Antti-Pyhaluoto/GPS-Project-TVT17SPL/GPS/GPS_encode_v1.cpp

#include "mbed.h"
#include <string>
#include "math.h"


Serial gsm(D14, D15);
Serial pc(SERIAL_TX, SERIAL_RX);



int main()
{
    
    pc.baud(9600);
    
    pc.printf("Käynnistys");
    
    
    while(true) {
		pc.printf("LOOPIN ALKU!\n\n\n");
		char buffer[450];
		for(int i = 0; i< 450; i++)
		{
		
		char c = gsm.getc();
		
		buffer[i] = c;
		
		
		}
		//pc.puts(buffer);
		
		
		
		//Haluttu input = "$GPGVA,111604.00,6500.02320,N,02530.55534,E,1,05,3.74,24.8,M,20.9,M,,*69";
		
		char *token;		
		token = strtok(buffer, "$");
		
		//pc.printf("TYHJÄ = %s\n", token);
			
		char* paikannusTieto = {"GPGGA"};
	
		while (true){
			
		bool loyty = false;
		
		token = strtok(NULL, "$");
		//pc.printf("koko = %s\n", token);
						
		for(int i = 0; i < 5; i++)
		{
			if (paikannusTieto[i] != token[i])
			{
				//pc.printf("Väärä merkki!\n");
				loyty = true;
				break;
			}
		}
		if (!loyty){
			
		break;
		}
		
	}
		while (gsm.readable())
		{
		char c = gsm.getc();
		}
		token = strtok(token, ",.");
		//pc.printf("mikä tämä on? = %s\n", token);
			
		token = strtok(NULL, ",.");
		//pc.printf("token = %s\n", token);
		int fix = atoi(token);
		int aika = fix + 20000;
		
		token = strtok(NULL, ",.");
		//pc.printf("token = %s\n", token);
		int nolla = atoi(token);
		
		token = strtok(NULL, ",.");
		//pc.printf("token = %s\n", token);
		int kulma = (atoi(token));					//JAA 100
		float todellinenKulma = kulma/100;			// 65 !!
		
		token = strtok(NULL, ",.");
		//pc.printf("token = %s\n", token);
		float minuutit = atoi(token);
		float todellisetMinuutit = minuutit/100000;	//0.0232000
		
		float latitude = todellinenKulma + (todellisetMinuutit / 60);
		
		token = strtok(NULL, ",.");
		//pc.printf("token = %s\n", token);
		int Korkeus = atoi(token);
		
		token = strtok(NULL, ",.");
		//pc.printf("token = %s\n", token);
		float a6 = atoi(token);						//2530.000000				
		float LeveysKulma = a6/100;
		LeveysKulma = floor(LeveysKulma);			//Pyöristää kahden desimaalin kokonaisluvuksi
		
		float valivaihe = a6 - (LeveysKulma * 100);	// = 30 MINUUTIT
		
		
		token = strtok(NULL, ",.");
		//pc.printf("token = %s\n", token);
		float a7 = atoi(token);
		float leveydenAika= a7/100000;				// 0,55534
		
		float longitude = LeveysKulma + (valivaihe + leveydenAika) / 60;
		
		token = strtok(NULL, ",.");
		//pc.printf("token = %s\n", token);			//EAST
		int leveysSuunta = atoi(token);
		
		token = strtok(NULL, ",.");
		//pc.printf("token = %s\n", token);
		int a9 = atoi(token);
		
		token = strtok(NULL, ",.");
	//	pc.printf("token = %s\n", token);
		int a10 = atoi(token);
		
		token = strtok(NULL, ",.");
	//	pc.printf("token = %s\n", token);
		int a11 = atoi(token);
		
		token = strtok(NULL, ",.");
	//	pc.printf("token = %s\n", token);
		int a12 = atoi(token);
	 
		
		
		//pc.printf("aika=%d\n nolla=%d\n todellinenKulma=%f\n todellisetMinuutit=%f\n Korkeus=%d\n LeveysKulma= %f\n a7=%f\n leveysSuunta=%d\n a9=%d a10=%d\n a11=%d; a12=%d a13=%d; a14=%d; a15=%d a16=%d; a17=%d; a18=%d; a19=d;\n", aika,nolla,todellinenKulma,todellisetMinuutit,Korkeus,LeveysKulma,a7,leveysSuunta,a9);
		
		pc.printf("aika = %d\n longitude = %f\n Latitude = %f\n\n\n\n",aika, longitude, latitude);
	}
}
